effevee/effevees_rover/documentatie/rover02.jpg

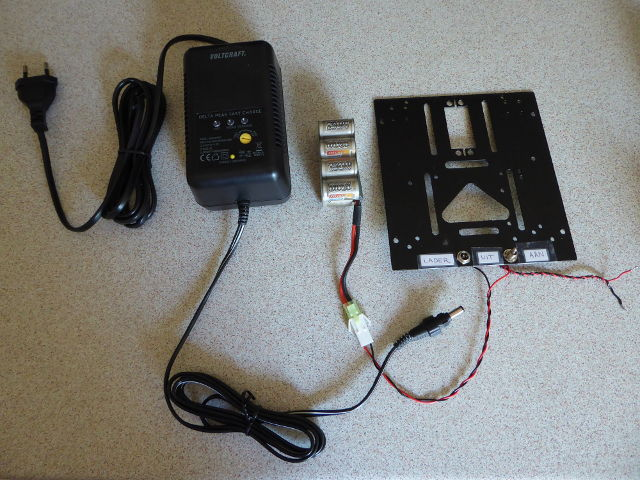
documentatie/rover02.jpg
