effevee/effevees_rover/documentatie/rover05.jpg

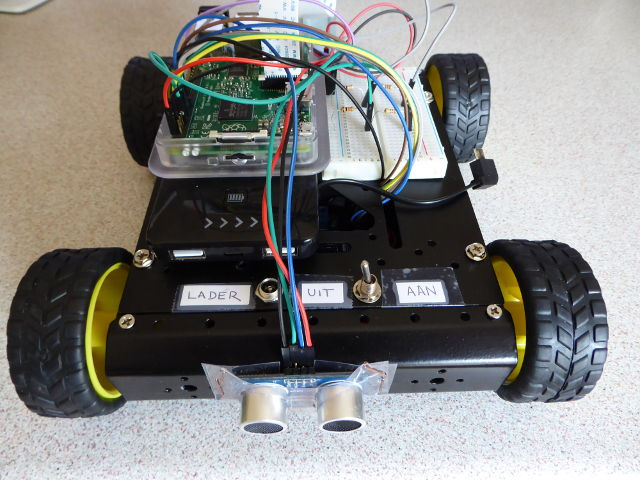
documentatie/rover05.jpg
