effevee/effevees_rover/documentatie/rover08.jpg

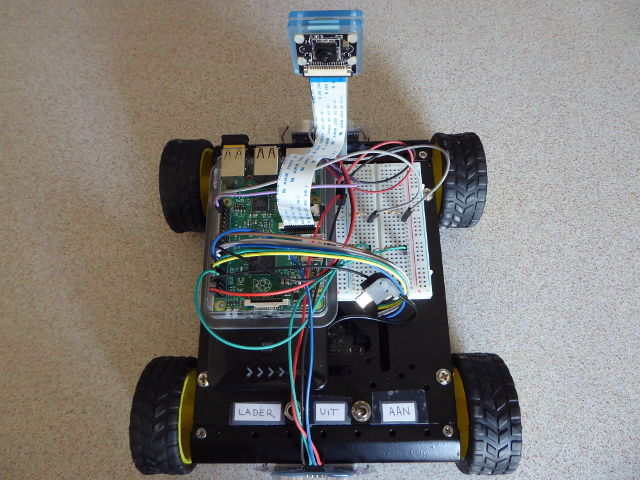
documentatie/rover08.jpg
