effevee/effevees_rover/templates/knop-auto.png

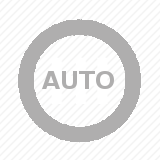
templates/knop-auto.png
