effevee/effevees_rover/templates/pijl-achteruit.png

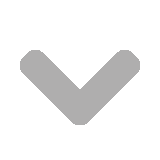
templates/pijl-achteruit.png
