effevee/effevees_rover/templates/pijl-rechts.png

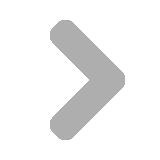
templates/pijl-rechts.png
