effevee/effevees_rover/templates/pijl-vooruit.png

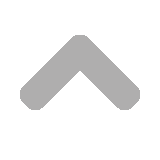
templates/pijl-vooruit.png
