effevee/effevees_rover/templates/stoppen.png

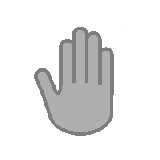
templates/stoppen.png
